pan0ne/CO2-Ampel/docs/01. Amica_prepare4Display.jpg

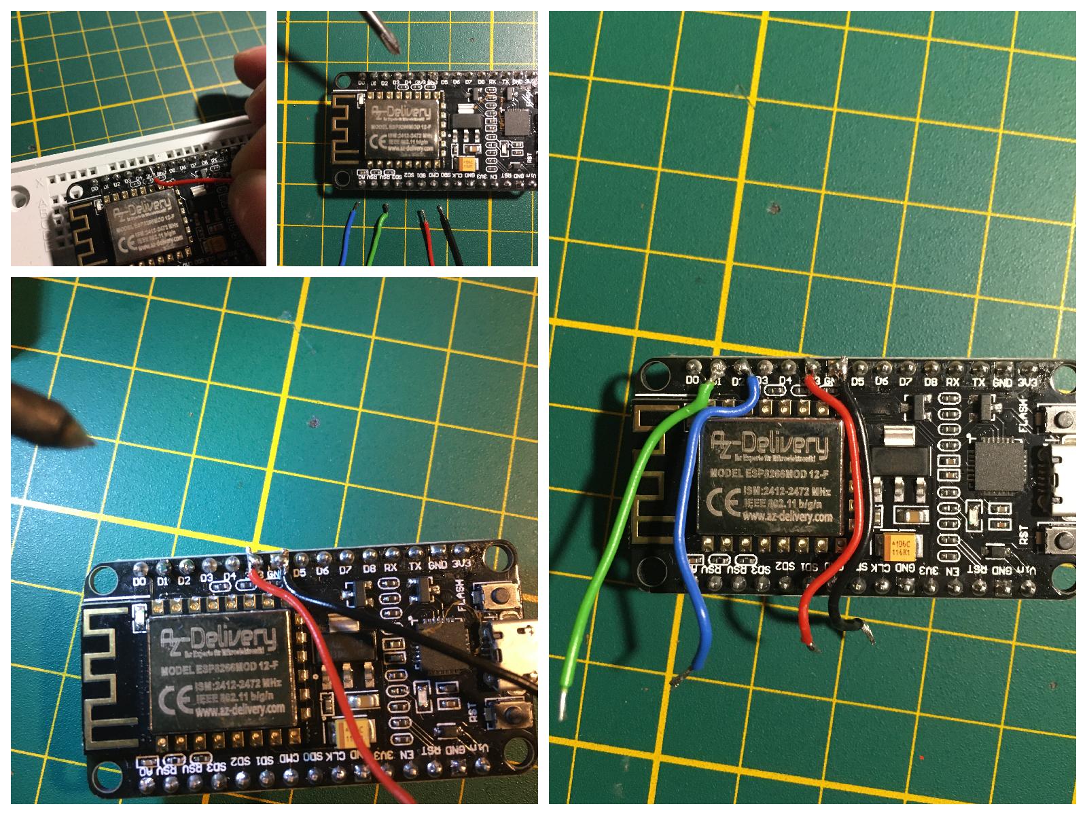
docs/01. Amica_prepare4Display.jpg
