pan0ne/CO2-Ampel/docs/01. Display2Amica.jpg

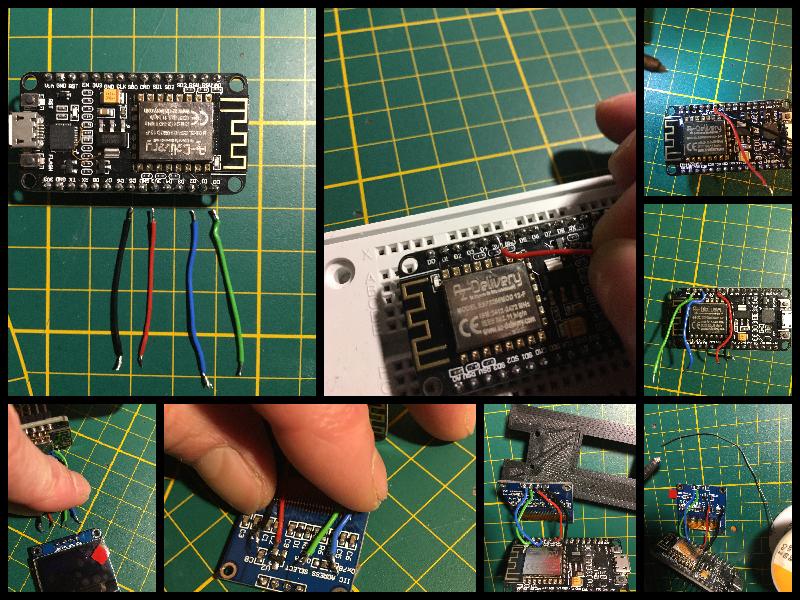
docs/01. Display2Amica.jpg
