pan0ne/CO2-Ampel/docs/02. Case-CO2-Sensor.jpg

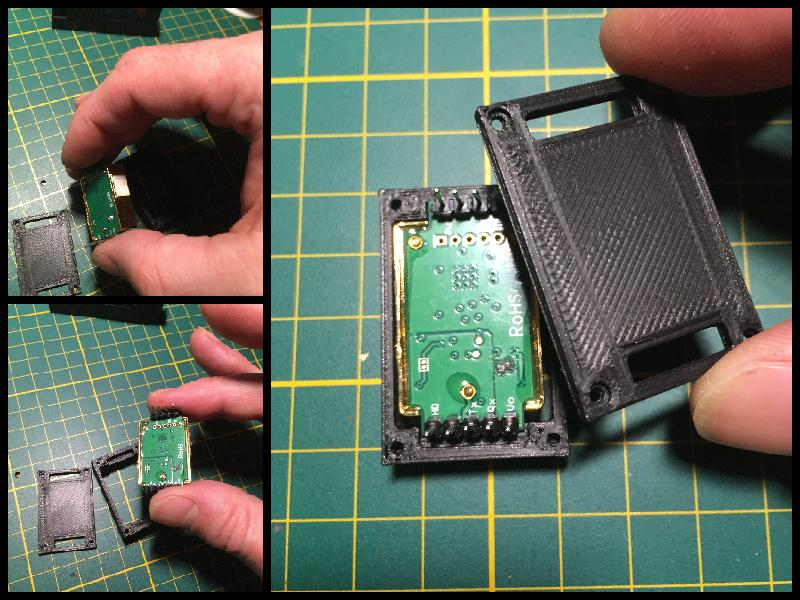
docs/02. Case-CO2-Sensor.jpg
