pan0ne/CO2-Ampel/docs/03. Module2Mainbox.jpg

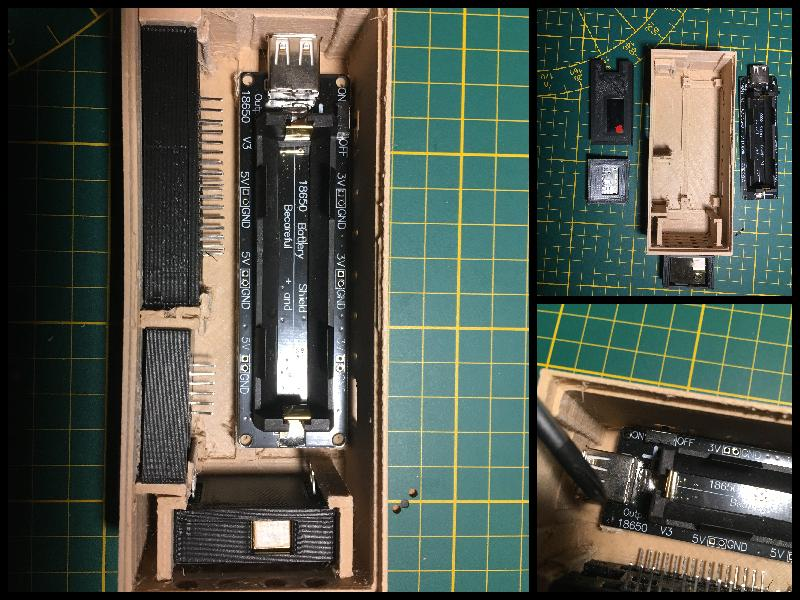
docs/03. Module2Mainbox.jpg
