pan0ne/CO2-Ampel/docs/04. Verkabelung.jpg

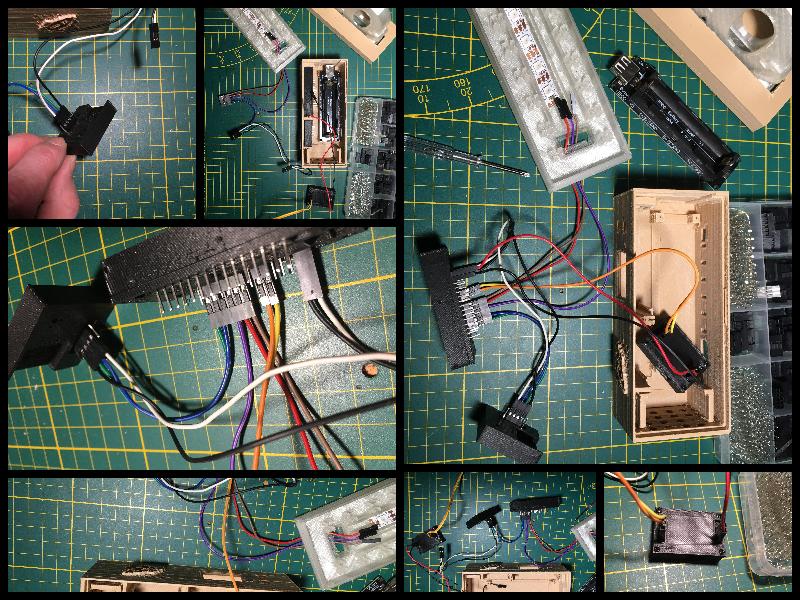
docs/04. Verkabelung.jpg
