pan0ne/CO2-Ampel/docs/05. Module2Cable2Box.jpg

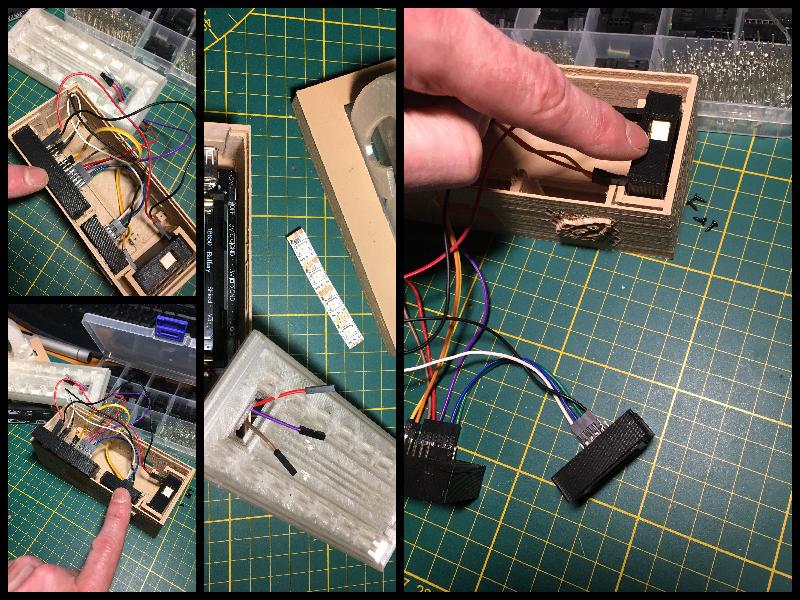
docs/05. Module2Cable2Box.jpg
