pan0ne/CO2-Ampel/docs/06. Neopixel.jpg

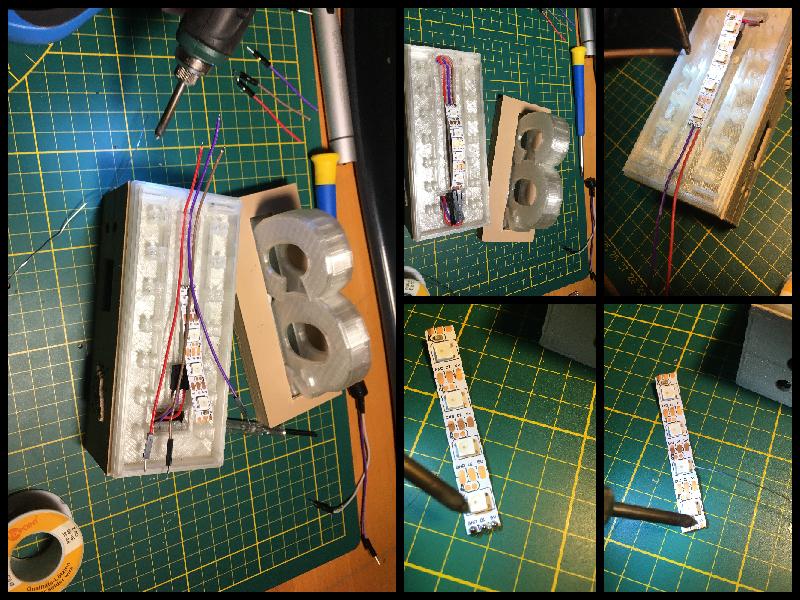
docs/06. Neopixel.jpg
