pan0ne/CO2-Ampel/docs/07. CloseUp.jpg

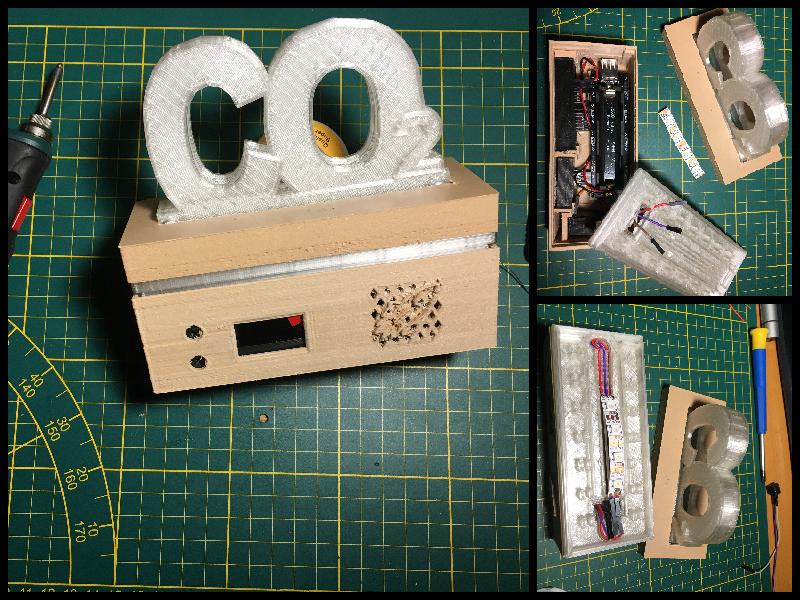
docs/07. CloseUp.jpg
