pan0ne/CO2-Ampel/docs/Amica2Display.jpg

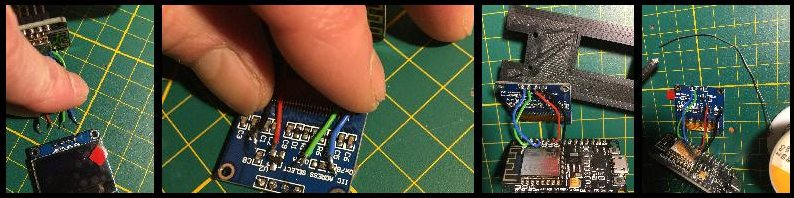
docs/Amica2Display.jpg
