pan0ne/CO2-Ampel/docs/Anschlussdiagramme/Anschluss_Amica2.jpg

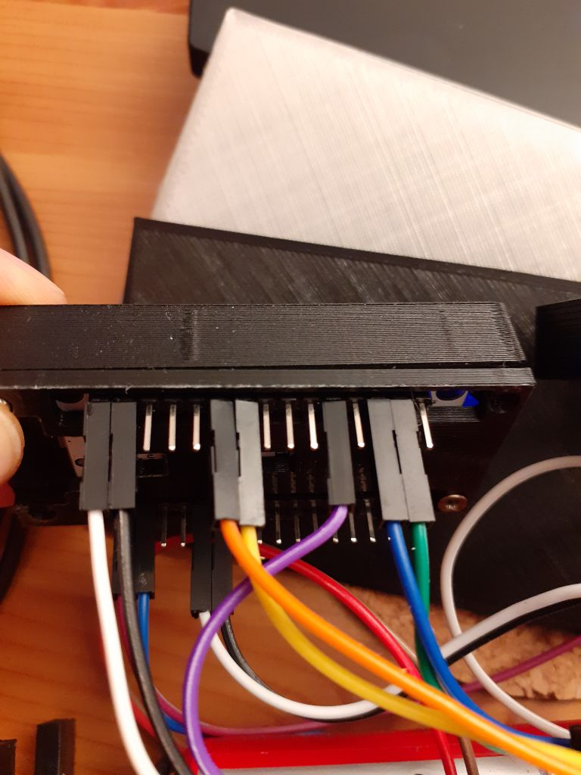
docs/Anschlussdiagramme/Anschluss_Amica2.jpg
