pan0ne/CO2-Ampel/docs/Anschlussdiagramme/Anschluss_Amica.jpg

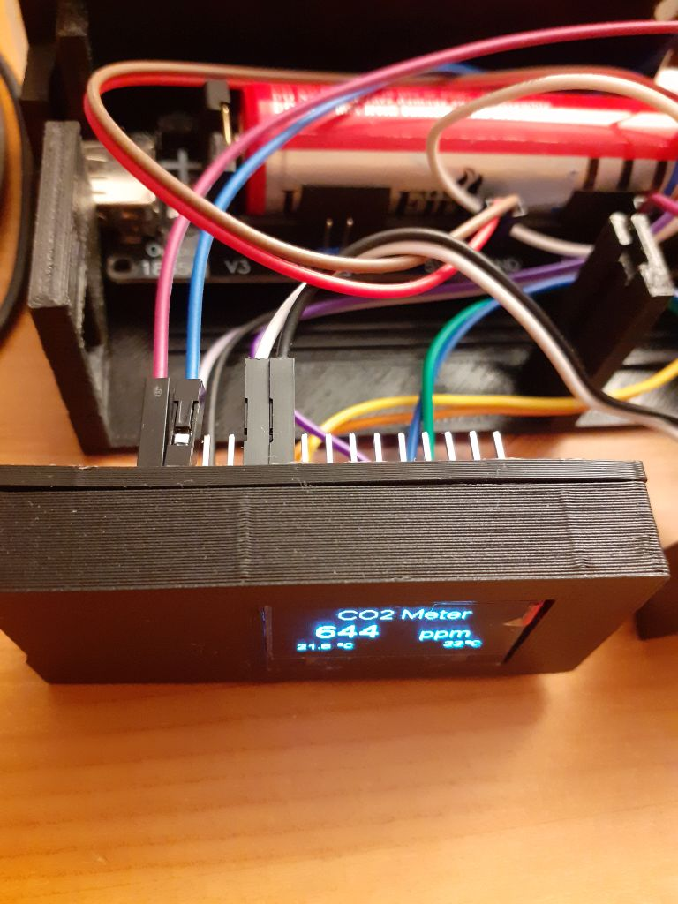
docs/Anschlussdiagramme/Anschluss_Amica.jpg
