pan0ne/CO2-Ampel/docs/Anschlussdiagramme/CO2 Ampel Boardverwaltung.png

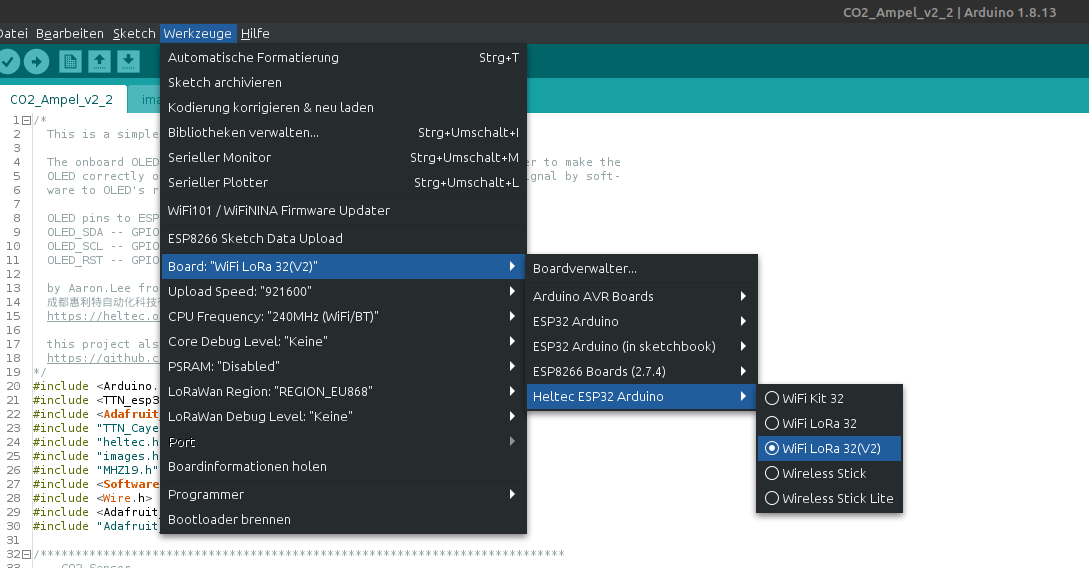
docs/Anschlussdiagramme/CO2 Ampel Boardverwaltung.png
