pan0ne/CO2-Ampel/docs/Anschlussdiagramme/CO2-Ampel_Anschluss_Esp8266-MH-Z19b.png

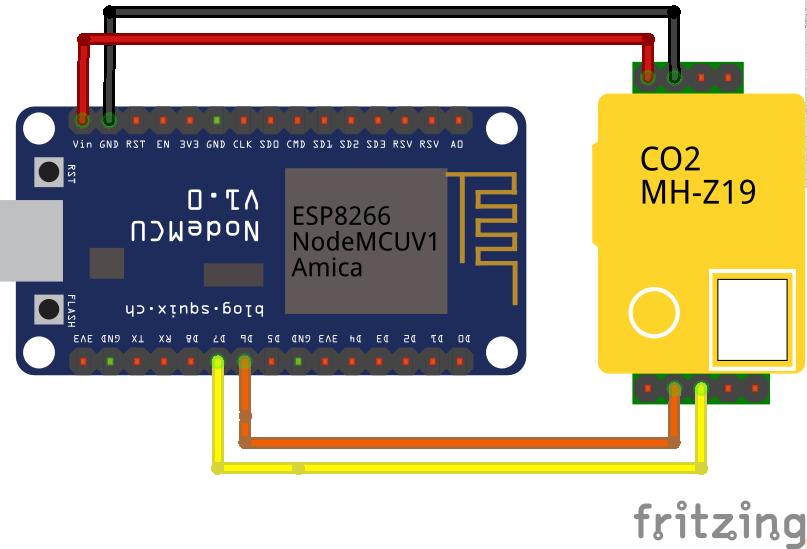
docs/Anschlussdiagramme/CO2-Ampel_Anschluss_Esp8266-MH-Z19b.png
