pan0ne/CO2-Ampel/docs/Anschlussdiagramme/CO2-Ampel_ESP8266_Anschlussplan_alle-Sensoren.png

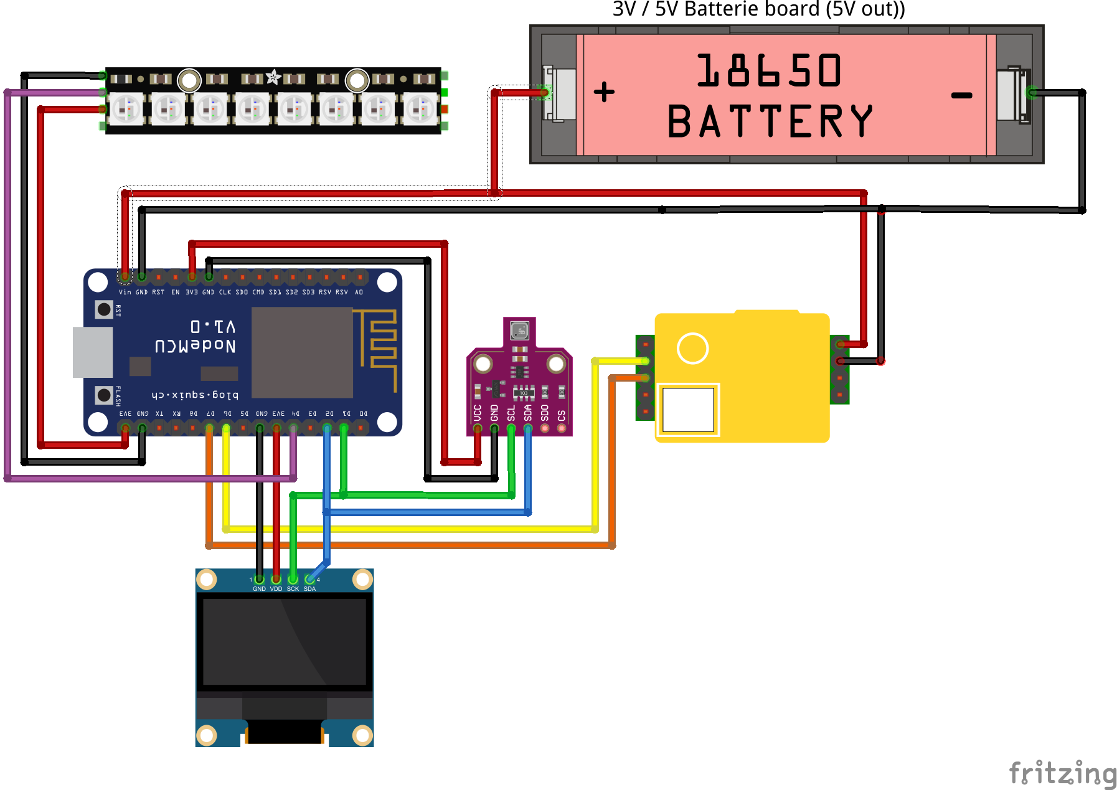
docs/Anschlussdiagramme/CO2-Ampel_ESP8266_Anschlussplan_alle-Sensoren.png
