pan0ne/CO2-Ampel/docs/Anschlussdiagramme/SSD1306-NodeMCUv2.png

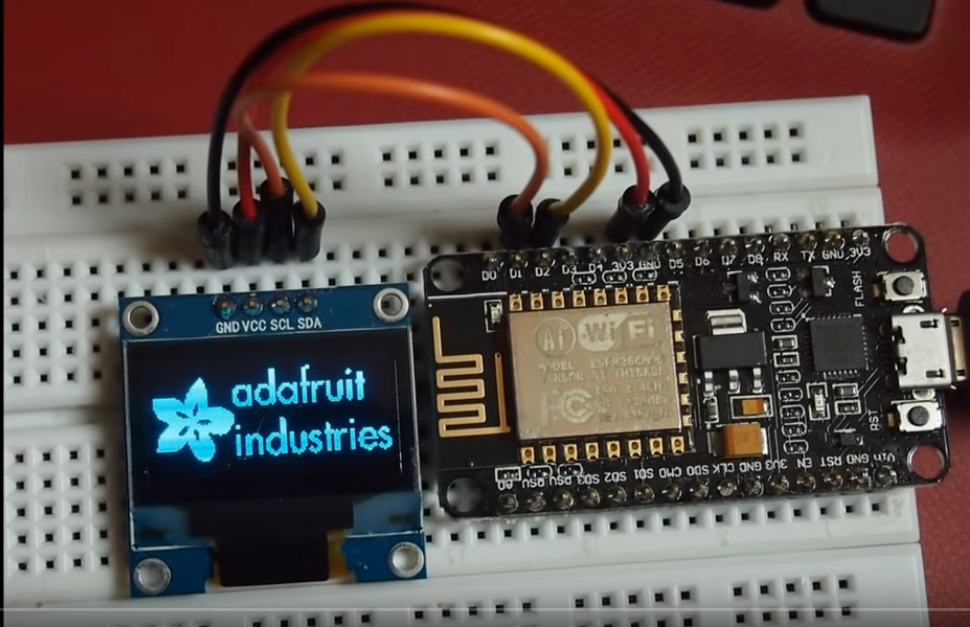
docs/Anschlussdiagramme/SSD1306-NodeMCUv2.png
