pan0ne/CO2-Ampel/docs/Arduino_Sketch-Ansicht-Boardverwaltung.jpg

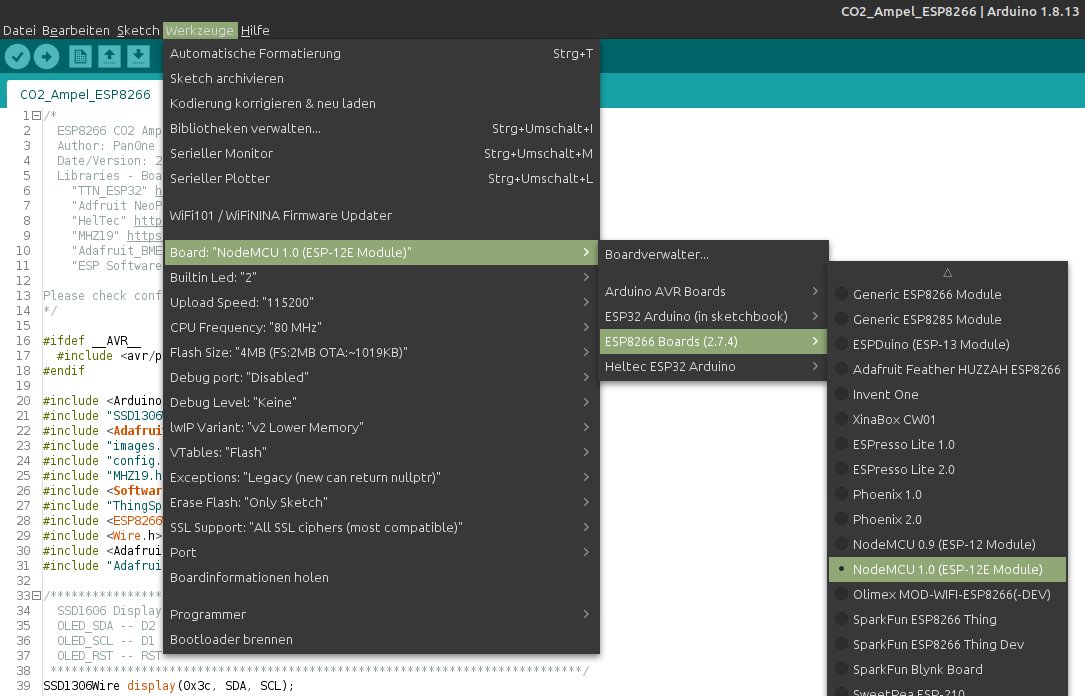
docs/Arduino_Sketch-Ansicht-Boardverwaltung.jpg
