pan0ne/CO2-Ampel/docs/Arduino_Sketch-Ansicht-NewTab.png

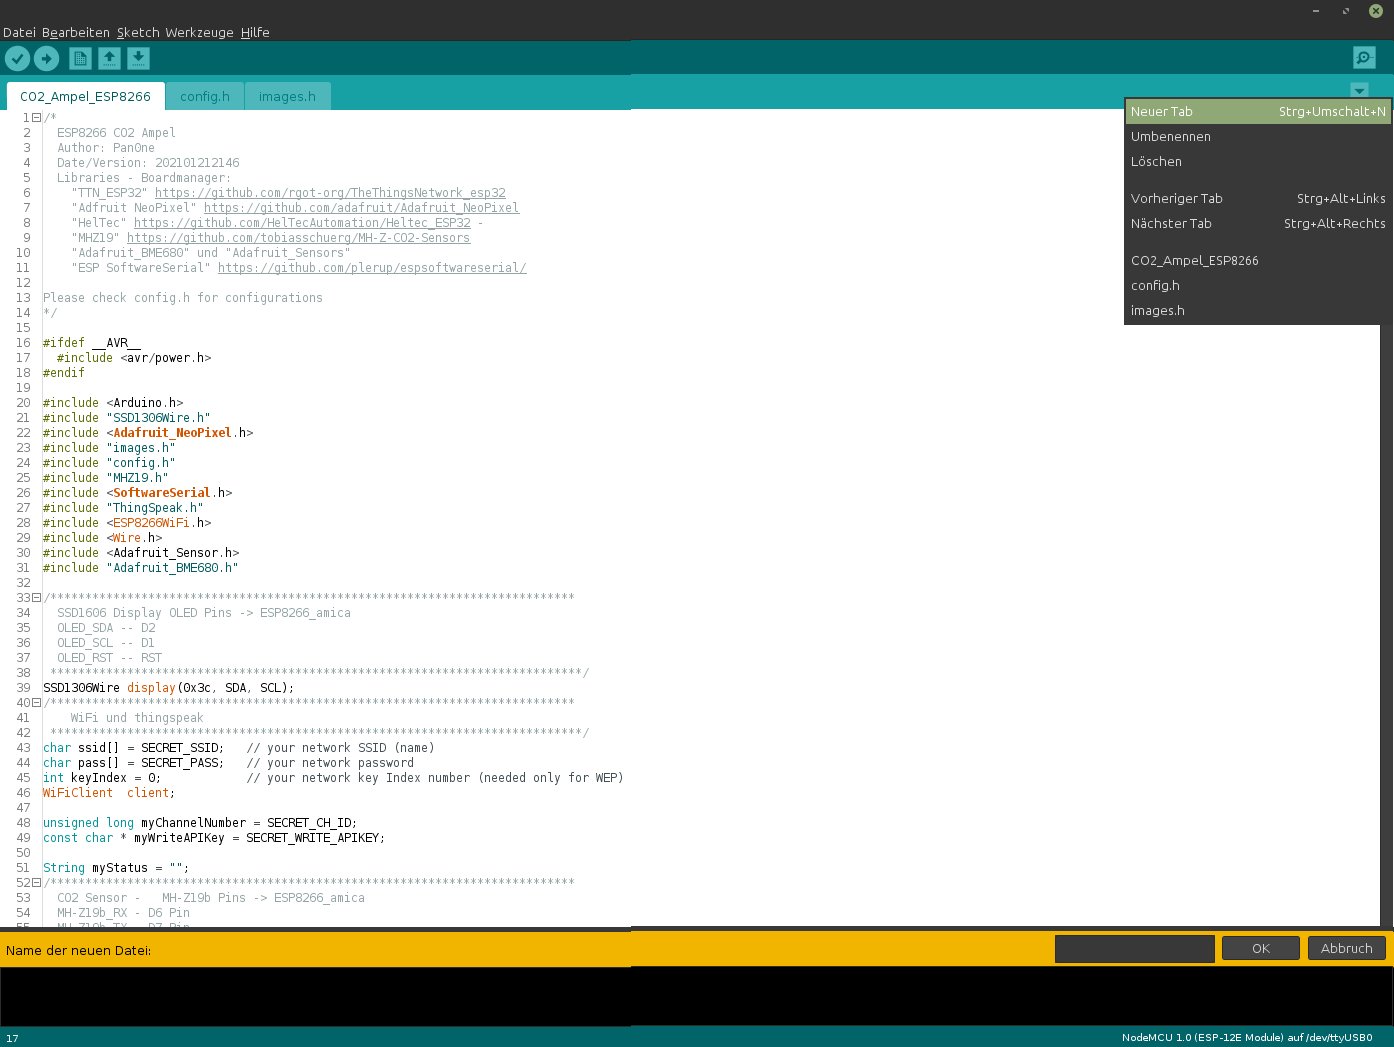
docs/Arduino_Sketch-Ansicht-NewTab.png
