pan0ne/CO2-Ampel/docs/Arduino_Sketch-Ansicht-Tabs.png

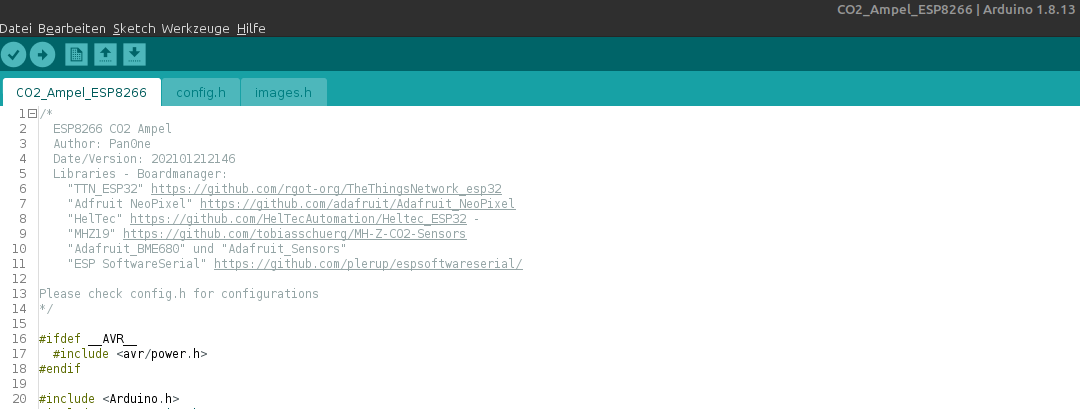
docs/Arduino_Sketch-Ansicht-Tabs.png
