pan0ne/CO2-Ampel/docs/Batterie-Shield_LiPo18650.jpeg

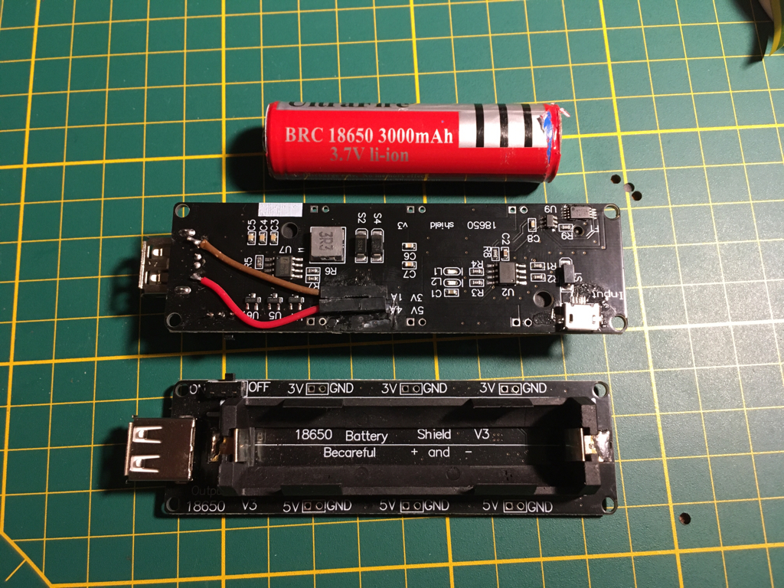
docs/Batterie-Shield_LiPo18650.jpeg
