pan0ne/CO2-Ampel/docs/CO2-Ampel_Elektronische_Bauteile2.jpg

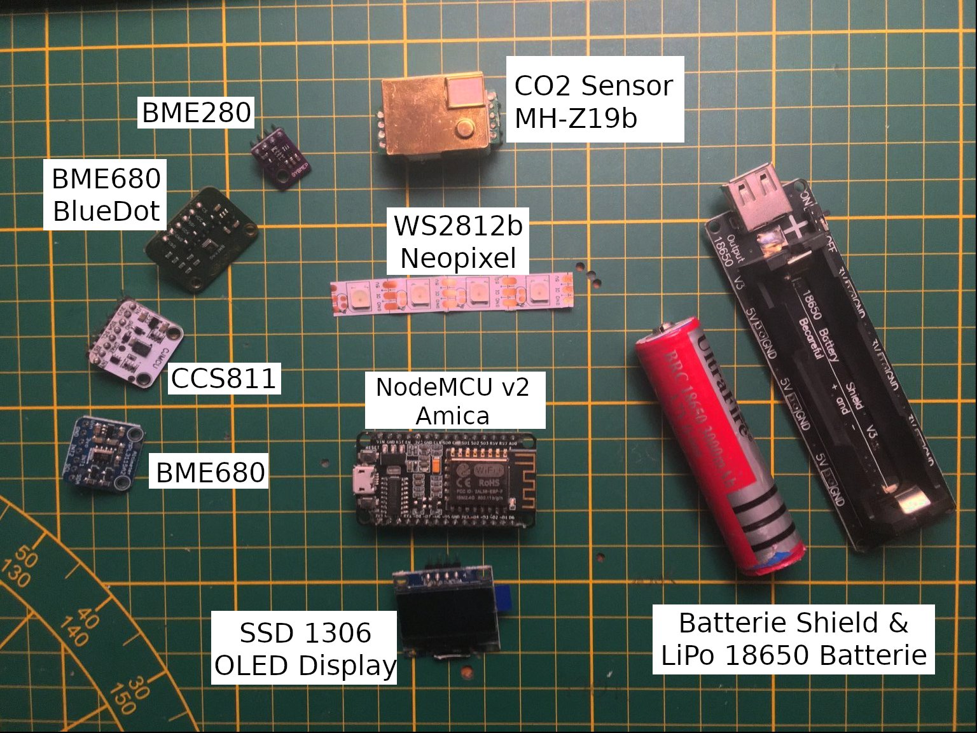
docs/CO2-Ampel_Elektronische_Bauteile2.jpg
