pan0ne/CO2-Ampel/docs/ESP8266mitSSD1306Display.png

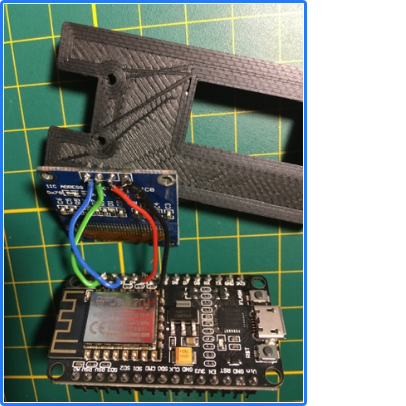
docs/ESP8266mitSSD1306Display.png
