pan0ne/CO2-Ampel/docs/Gedruckte_Bauteile2.jpg

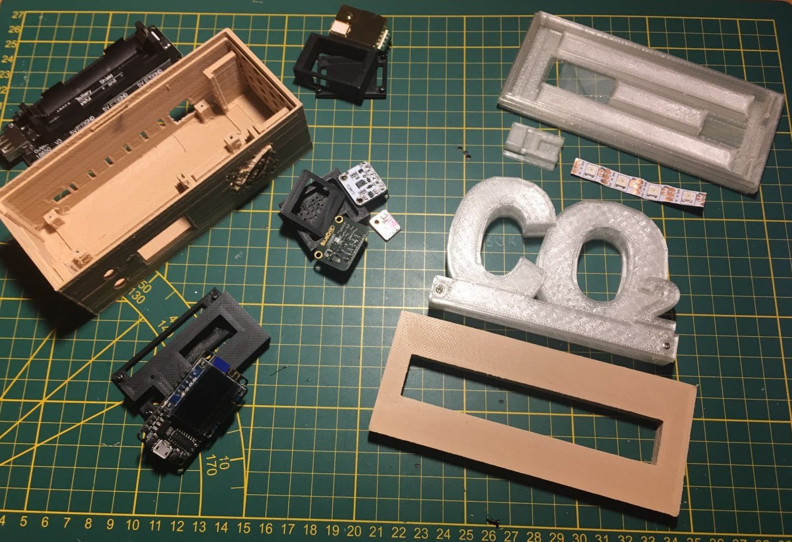
docs/Gedruckte_Bauteile2.jpg
