pan0ne/CO2-Ampel/docs/IMG_2711.JPG

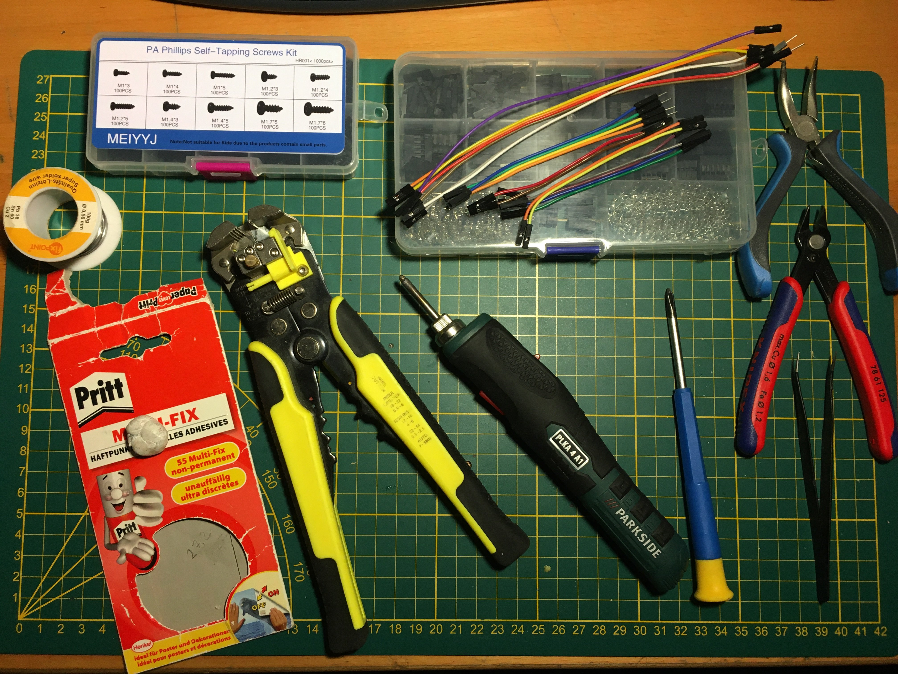
docs/IMG_2711.JPG
