pan0ne/CO2-Ampel/images/CO2-Ampel-Display.800.jpg

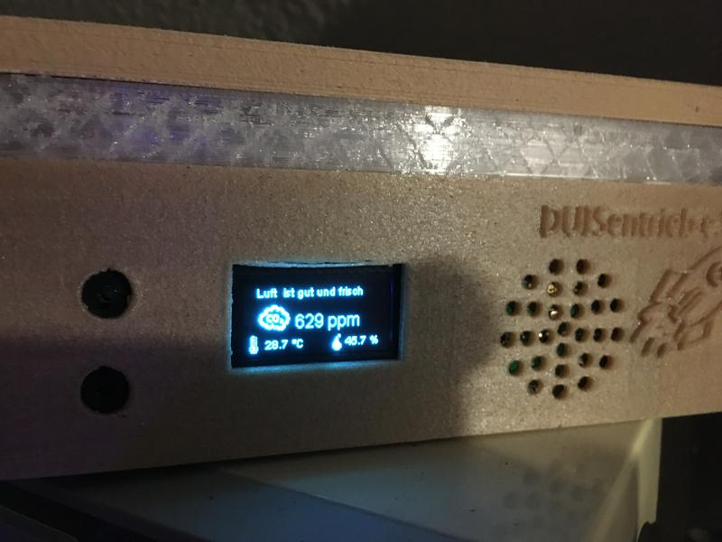
images/CO2-Ampel-Display.800.jpg
