pan0ne/CO2-Ampel/code/co2-ampel_esp8266.ino

/*
*  ESP8266 CO2 Ampel
*  Author: Pan0ne
*  Libraries - Boardmanager:
*    "TTN_ESP32" https://github.com/rgot-org/TheThingsNetwork_esp32
*    "Adfruit NeoPixel" https://github.com/adafruit/Adafruit_NeoPixel
*    "MHZ19" https://github.com/tobiasschuerg/MH-Z-CO2-Sensors
*    "Adafruit_BME680" und "Adafruit_Sensors"
*    "ESP SoftwareSerial" https://github.com/plerup/espsoftwareserial/
*    "WifiManager" https://github.com/tzapu/WiFiManager
*    
*    Please include and images.h and config.h 
*    In config.h, the variables for Wifi, the number of neopixels, Thingspeak API keys, 
*    sensor pins and values for temperature adjustment are defined.
*/

#ifdef __AVR__
  #include <avr/power.h>
#endif

#include <Arduino.h>
#include "SSD1306Wire.h"
#include <Adafruit_NeoPixel.h>
#include "images.h"
#include "config.h"
#include "MHZ19.h"
#include <SoftwareSerial.h>
#include "ThingSpeak.h"
#include <ESP8266WiFi.h>
#include <WiFiManager.h> 
#include <Wire.h>
#include <Adafruit_Sensor.h>
#include "Adafruit_BME680.h"

/***************************************************************************
  SSD1606 Display OLED Pins -> ESP8266_amica
  OLED_SDA -- D2
  OLED_SCL -- D1
  OLED_RST -- RST
 ****************************************************************************/
SSD1306Wire display(0x3c, SDA, SCL);
/***************************************************************************
    WiFi und thingspeak
 ****************************************************************************/
// char ssid[] = SECRET_SSID;   // your network SSID (name)
// char pass[] = SECRET_PASS;   // your network password
int keyIndex = 0;            // your network key Index number (needed only for WEP)
WiFiClient  client;

void configModeCallback (WiFiManager *myWiFiManager) {
  Serial.println("Entered config mode");
  Serial.println(WiFi.softAPIP());
  //if you used auto generated SSID, print it
  Serial.println(myWiFiManager->getConfigPortalSSID());
}

unsigned long myChannelNumber = SECRET_CH_ID;
const char * myWriteAPIKey = SECRET_WRITE_APIKEY;

String myStatus = "";
/***************************************************************************
  CO2 Sensor -   MH-Z19b Pins -> ESP8266_amica
  MH-Z19b_RX - D6 Pin
  MH-Z19b_TX - D7 Pin
 ****************************************************************************/
unsigned long getDataTimer = 0;
MHZ19 myMHZ19;          // Constructor for library
SoftwareSerial mySerial(RX_PIN, TX_PIN);                   // (Uno example) create device to MH-Z19 serial
//HardwareSerial mySerial(1);
int8_t Temp;
int CO2;

/***************************************************************************
 Button handler (FlashButton als normalen Inputbutton verwenden)
 ****************************************************************************/
void IRAM_ATTR handleInterrupt() {
  dMode++;
}
/***************************************************************************
  BME 680 Sensor / Pins -> ESP8266_amica
  SDA - D2 (GPIO 2)
  SCL - D1 (GPIO 1) 
 ****************************************************************************/
#define SEALEVELPRESSURE_HPA (1013.25)
Adafruit_BME680 bme; // I2C

float hum_weighting = 0.25; // so hum effect is 25% of the total air quality score
float gas_weighting = 0.75; // so gas effect is 75% of the total air quality score

int   humidity_score, gas_score;
float gas_reference = 2500;
float hum_reference = 40;
int   getgasreference_count = 0;
int   gas_lower_limit = 10000;  // Bad air quality limit
int   gas_upper_limit = 300000; // Good air quality limit
String  air_quality;
/***************************************************************************
    Logo "co2a_logo" -> images.h
    Duisentrieb Logo und Schriftzug
 ****************************************************************************/
void logo()
{
  display.clear();
  display.drawXbm(85, 2, logo_width, logo_height, co2a_logo);
  display.setFont(ArialMT_Plain_10);
  display.drawString(15, 15, "DUISentrieb");
  delay(1000);
  display.setFont(ArialMT_Plain_24);
  display.drawString(2, 35, "CO2 Ampel");
  display.display();
  delay(6000);
}
/***************************************************************************  
  Neopixel / Pin -> ESP8266_amica
  Di - D5 (GPIO 25)
 ****************************************************************************/
// NUMPIXELS -> the count of neopixels is defined in the config.h 
Adafruit_NeoPixel pixels(NUMPIXELS, PIN, NEO_GRB + NEO_KHZ800);
#define DELAYVAL 500 // Time (in milliseconds) to pause between pixels

// Rainbow cycle along whole strip. Pass delay time (in ms) between frames.
void rainbow(int wait) {

  for (long firstPixelHue = 0; firstPixelHue < 5 * 65536; firstPixelHue += 256) {
    for (int i = 0; i < pixels.numPixels(); i++) { // For each pixel in strip...
      // (strip.numPixels() steps):
      int pixelHue = firstPixelHue + (i * 65536L / pixels.numPixels());
      pixels.setPixelColor(i, pixels.gamma32(pixels.ColorHSV(pixelHue)));
    }
    pixels.show(); // Update strip with new contents
    delay(wait);  // Pause for a moment
  }
}

void colorWipe(uint32_t color, int wait) {
  for (int i = 0; i < pixels.numPixels(); i++) { // For each pixel in strip...
    pixels.setPixelColor(i, color);         //  Set pixel's color (in RAM)
    pixels.show();                          //  Update strip to match
    delay(wait);                           //  Pause for a moment
  }
}
/***************************************************************************
    Setup
 ****************************************************************************/
void setup()
{
  Serial.begin(9600);

  #if defined (__AVR_ATtiny85__)
  if (F_CPU == 16000000) clock_prescale_set(clock_div_1);
  #endif

  pixels.begin();
  pixels.setBrightness(35); 
  Wire.begin();
  bme.begin();

    if (!bme.begin()) {
      Serial.println("Could not find a valid BME680 sensor, check wiring!");
    } else {
      Serial.println("Found a sensor");
    }

  // Set up oversampling and filter initialization
  bme.setTemperatureOversampling(BME680_OS_8X);
  bme.setHumidityOversampling(BME680_OS_2X);
  bme.setPressureOversampling(BME680_OS_4X);
  bme.setIIRFilterSize(BME680_FILTER_SIZE_3);
  bme.setGasHeater(320, 150); // 320*C for 150 ms
  delay(500);
  bme.performReading();
  delay(500);
  GetGasReference();

  colorWipe(pixels.Color(  0, 150,   150), 40); // Blue
  //SSD1306_SWITCHCAPVCC = generate display voltage from 3.3V internally

  // Initialising the UI will init the display too.
  display.init();

  display.flipScreenVertically();
  display.setFont(ArialMT_Plain_10);

  // Show initial display buffer contents on the screen --
  // the library initializes this with an Adafruit splash screen.
  display.clear();
  delay(2000); // Pause for 2 seconds

  // Clear the buffer
  display.clear();

  logo();
  colorWipe(pixels.Color(  255, 71,   0), 40); // Orange

/* Old Wifi connecting mode
 *  

WiFi.mode(WIFI_STA);
  WiFi.begin(ssid, pass);

  while (WiFi.status() != WL_CONNECTED) {
    delay(500);
    Serial.print(".");
  }

  Serial.println("");
  Serial.println("WiFi connected");
  Serial.println("IP address: ");
  Serial.println(WiFi.localIP());
  String ipString = WiFi.localIP().toString();
 */

  // WiFiManager
  //Local intialization. Once its business is done, there is no need to keep it around
  WiFiManager wifiManager;
  //reset settings - for testing
  //wifiManager.resetSettings();

  //set callback that gets called when connecting to previous WiFi fails, and enters Access Point mode
  wifiManager.setAPCallback(configModeCallback);

  //fetches ssid and pass and tries to connect
  //if it does not connect it starts an access point with the specified name
  //here  "AutoConnectAP"
  //and goes into a blocking loop awaiting configuration
  if(!wifiManager.autoConnect()) {
    Serial.println("failed to connect and hit timeout");
    //reset and try again, or maybe put it to deep sleep
    ESP.restart();
    delay(1000);
  } 

  //if you get here you have connected to the WiFi
  Serial.println("WIFI connected...:)");
 
  display.clear();
  display.setTextAlignment(TEXT_ALIGN_CENTER);
  display.setFont(ArialMT_Plain_16);
  display.drawString(60, 0, "WiFi verbunden");
  colorWipe(pixels.Color(  0, 63,   0), 70); // Green
  //display.drawString(60,20, String(ipString));
  display.display();
  delay(3000);

  mySerial.begin(BAUDRATE);          // Uno Example: Begin Stream with MHZ19 baudrate
  myMHZ19.begin(mySerial);
  myMHZ19.autoCalibration(true);   // Turn auto calibration ON (OFF autoCalibration(false))
 
  pinMode(FlashButtonPIN, INPUT_PULLUP);
  attachInterrupt(digitalPinToInterrupt(FlashButtonPIN), handleInterrupt, FALLING);
  
  ThingSpeak.begin(client);  // Initialize ThingSpeak
  delay(3000);
}


void loop()
{
    if (dMode != last_dMode) { 
    display.clear();
    display.setTextAlignment(TEXT_ALIGN_CENTER);
    display.setFont(ArialMT_Plain_16);
    display.drawString(60, 20, "Kalibrierung \n gestartet");
    display.display(); 
    myMHZ19.calibrateZero();
    delay(5000);
    display.clear();
    display.drawString(60, 20, "Kalibrierung \n erfolgreich!");
    display.display();
    delay(2000);    
    last_dMode = dMode;
  }
  
  display.clear();
  display.setTextAlignment(TEXT_ALIGN_CENTER);
  display.setFont(ArialMT_Plain_16);
  //display.drawXbm(60, 0, co2_width, co2_height, co2_sym);
  display.drawString(65, 0, "CO2 Meter");

  display.setTextAlignment(TEXT_ALIGN_RIGHT);
  display.setFont(ArialMT_Plain_16);
  display.drawString(110, 30, " ppm");
  display.display();
  display.setTextAlignment(TEXT_ALIGN_LEFT);
  display.setFont(ArialMT_Plain_24);
  readMHZ19b();
  Temp = myMHZ19.getTemperature();          // Request CO2 (as ppm)
  display.drawString(15, 20, String(CO2));

  display.setTextAlignment(TEXT_ALIGN_LEFT);
  display.setFont(ArialMT_Plain_10);
  display.drawString(5, 50, String(bme.readTemperature() + temp_adjust, 1)     + " ° C");

  display.setTextAlignment(TEXT_ALIGN_RIGHT);
  display.setFont(ArialMT_Plain_10);
  //display.drawString(120, 50, String(Temp) + "°C");
  display.drawString(120, 50, String(bme.readHumidity(), 1)        + "%");

  display.display();
  co2Warnung();


 /* if (digitalRead(T4) == 1){
    display.clear();
    display.setTextAlignment(TEXT_ALIGN_LEFT);
    display.setFont(ArialMT_Plain_10);
    display.drawString(5, 2, " Temperature = " + String(bme.readTemperature(), 2)     + "°C");
    display.drawString(5, 12, " Pressure = " + String(bme.readPressure() / 100.0F) + " hPa");
    display.drawString(5, 22, " Humidity = " + String(bme.readHumidity(), 1)        + "%");
  */
    humidity_score = GetHumidityScore();
    gas_score      = GetGasScore();


    //Combine results for the final IAQ index value (0-100% where 100% is good quality air)
    float air_quality_score = humidity_score + gas_score;
    if ((getgasreference_count++) % 5 == 0) GetGasReference();

    air_quality = CalculateIAQ(air_quality_score);
    //display.setTextAlignment(TEXT_ALIGN_CENTER);
    //display.setFont(ArialMT_Plain_10);
    //display.drawString(5, 33, String(air_quality));

   //display.display();
   delay(12000);

  // set the fields with the values
  ThingSpeak.setField(1, CO2);
  ThingSpeak.setField(2, bme.readTemperature());
  ThingSpeak.setField(3, bme.readHumidity());
  ThingSpeak.setField(4, air_quality_score);

  // set the status
  ThingSpeak.setStatus(myStatus);

  // write to the ThingSpeak channel
  int x = ThingSpeak.writeFields(myChannelNumber, myWriteAPIKey);
  if(x == 200){
    Serial.println("Channel update successful.");
    myStatus = String("Online");
  }
  else{
    Serial.println("Problem updating channel. HTTP error code " + String(x));
    myStatus = String("Offline");
  }
  //Serial.println();
  //Serial.print("Versorgungs- oder Batteriespannung:  ");
  // Betriebsspannung auslesen
  // genaue Spannung der Stromquelle, PIN A0 muss mit 3,3V Verbunden werden!
  //Serial.println(getBatteryVoltage());
  
}

void readMHZ19b()
{
  const int INTERVAL = 3000;
  static unsigned long previousMillis;
  static int counter;

  if (millis() - previousMillis > INTERVAL)
  {
    previousMillis = millis();

    Serial.print(F("CO2 und Temperatur lesen: "));
    Serial.println(counter);

    CO2 = myMHZ19.getCO2();           // Request CO2 (as ppm)
    Serial.print(F("CO2: "));
    Serial.println(CO2);

    Temp = myMHZ19.getTemperature();   // Request Temperature (as Celsius)
    Serial.print(F("Temp: "));
    Serial.println(Temp);

    counter++;

     if (counter > 10){
       counter = 0;
      }

      return;
  }
}
void co2Warnung()
{
        if(CO2 < 850) {
          colorWipe(pixels.Color(  0, 45,   0), 150); // Green 63 = 1/4 brightness 255 = full brightness
        } else {
        if(CO2 < 1500) {
          colorWipe(pixels.Color(  45, 45,   0), 150); // Yellow 63 = 1/4 brightness 255 = full brightness
           if((CO2 > 1400) && (CO2 < 1500 )) {
            tone(14, 800); // …spiele diesen Ton...
            delay(100); //…und zwar für eine Sekunde...
            tone(14, 600); // …spiele diesen Ton...
            delay(200); //…und zwar für eine Sekunde...
            tone(14, 400); // …spiele diesen Ton...
            delay(300); //…und zwar für eine Sekunde...
            noTone(14); // Ton abschalten
            }
        } else {
        if(CO2 < 2000) {
           colorWipe(pixels.Color(  45, 8,   0), 40); // Orange 63/18 = 1/4 brightness 255/73 = full brightness
            if((CO2 > 1900) && (CO2 < 2000 )) {
            tone(14, 800); // …spiele diesen Ton...
            delay(100); //…und zwar für eine Sekunde...
            tone(14, 600); // …spiele diesen Ton...
            delay(200); //…und zwar für eine Sekunde...
            tone(14, 400); // …spiele diesen Ton...
            delay(300); //…und zwar für eine Sekunde...
            noTone(14); // Ton abschalten
            }
        } else {
            colorWipe(pixels.Color(45,   0,   0), 150); // Red 63 = 1/4 brightness 255 = full brightness
            //rainbow(10);
            tone(14, 600); // …spiele diesen Ton...
            delay(200); //…und zwar für eine Sekunde...
            noTone(14); // Ton abschalten
            }
          }
        }
}

void GetGasReference() {
  // Now run the sensor for a burn-in period, then use combination of relative humidity and gas resistance to estimate indoor air quality as a percentage.
  Serial.println("Getting a new gas reference value");
  int readings = 10;
  for (int i = 1; i <= readings; i++) { // read gas for 10 x 0.150mS = 1.5secs
    gas_reference += bme.readGas();
  }
  gas_reference = gas_reference / readings;
  Serial.println("Gas Reference = "+String(gas_reference,3));
}

String CalculateIAQ(int score) {
  String IAQ_text = "Air is ";
  score = (100 - score) * 5;
  if      (score >= 301)                  IAQ_text += "Schädlich";
  else if (score >= 201 && score <= 300 ) IAQ_text += "Sehr Ungesund";
  else if (score >= 176 && score <= 200 ) IAQ_text += "Ungesund";
  else if (score >= 151 && score <= 175 ) IAQ_text += "Nichts für Ältere";
  else if (score >=  51 && score <= 150 ) IAQ_text += "OK";
  else if (score >=  00 && score <=  50 ) IAQ_text += "Gut";
  //display.setTextAlignment(TEXT_ALIGN_CENTER);
  //display.setFont(ArialMT_Plain_10);
  //display.drawString(60, 59, "IAQ Score = " + String(score) + ", ");
  return IAQ_text;
}

int GetHumidityScore() {  //Calculate humidity contribution to IAQ index
  float current_humidity = bme.readHumidity();
  if (current_humidity >= 38 && current_humidity <= 42) // Humidity +/-5% around optimum
    humidity_score = 0.25 * 100;
  else
  { // Humidity is sub-optimal
    if (current_humidity < 38)
      humidity_score = 0.25 / hum_reference * current_humidity * 100;
    else
    {
      humidity_score = ((-0.25 / (100 - hum_reference) * current_humidity) + 0.416666) * 100;
    }
  }
  return humidity_score;
}

int GetGasScore() {
  //Calculate gas contribution to IAQ index
  gas_score = (0.75 / (gas_upper_limit - gas_lower_limit) * gas_reference - (gas_lower_limit * (0.75 / (gas_upper_limit - gas_lower_limit)))) * 100.00;
  if (gas_score > 75) gas_score = 75; // Sometimes gas readings can go outside of expected scale maximum
  if (gas_score <  0) gas_score = 0;  // Sometimes gas readings can go outside of expected scale minimum
  return gas_score;
}
/*
float getBatteryVoltage(){
    //************ Measuring Battery Voltage ***********
    float sample1 = 0;
    // Get 100 analog read to prevent unusefully read
    for (int i = 0; i < 100; i++) {
        sample1 = sample1 + analogRead(A0); //read the voltage from the divider circuit
        delay(2);
    }
    sample1 = sample1 / 100;
    // REFERENCE_VCC is reference voltage of microcontroller 3.3v for esp8266 5v Arduino
    // BAT_RES_VALUE_VCC is the kohom value of R1 resistor
    // BAT_RES_VALUE_GND is the kohom value of R2 resistor
    // 1023 is the max digital value of analog read (1024 == Reference voltage)
    float batVolt = (sample1 * REFERENCE_VCC  * (BAT_RES_VALUE_VCC + BAT_RES_VALUE_GND) / BAT_RES_VALUE_GND) / 1023;
    return batVolt;
}*/
